Resaj/time2time/fw/t2t_fw/state_machine.cpp

/**********************************************************************
 * Project: Time2time
 * 
 * File description: This code file contains the parameters and 
 * functions for controlling the state machine and the different modes 
 * of the chronometer
 * 
 * Author: Rubén Espino San José
 * Puma Pride Robotics Team
 * 
 * License: Attribution-NonCommercial-ShareAlike 4.0
 * International (CC BY-NC-SA 4.0) 
 *********************************************************************/

/**********************************************************************
 * Includes
 *********************************************************************/

#include "buttons.h"
#include "buzzer.h"
#include "display.h"
#include "espnow_comm.h"
#include "led_rgb.h"
#include "pass_sensor.h"
#include "scheduler.h"
#include "state_machine.h"
#include "supply.h"
#include "t2t_data.h"

/**********************************************************************
 * Defines & enums
 *********************************************************************/

#define BEST_TIME_INIT_VALUE  1000000

enum program_state {
  INIT_STATE,
  MAIN_MENU,
  SET_NUM_LAPS,
  SELECT_END_NODE,
  RUN_MODE,
  COMM_ERROR,
  SHOW_INFO
};

enum program_substate {
  INIT_SUBSTATE,
  SHOW_LINKED_NODE,
  WAIT_FOR_ACTION,
  SEND_MODE_REQUEST,
  WAIT_FOR_CONFIRMATION,
  WAIT_FOR_LAPS_SELECTION,
  WAIT_FOR_NODE_SELECTION,
  WAIT_FOR_START,
  SHOW_TIME_WITHOUT_DETECTION,
  WAIT_FOR_DETECTION,
  SHOW_TIME_DETECTION,
  DETECTED_AND_SENSING_LOCKED,
  DETECTED_AND_SENSING_ACTIVED,
  SHOW_FINAL_TIME,
  FINISHED
};

enum mode2run {
  NORMAL_LAP_TIME_MODE,
  X_LAPS_TIME_MODE,
  TIME_TRIAL_MODE,
  START_STOP_MODE,
  TOAST_MODE,
  SHOW_T2T_INFO,
  ONLY_CHARGE
};

enum nodeSelectionState {
  ERROR_WHILE_SELECTING = -1,
  SELECTION_IN_PROGRESS = 0,
  NODE_SELECTED = 1
};

typedef void (*function)(void);

typedef struct {
  mode2run          time_mode;
  char              text_in_menu[22];
  function          func;
  program_state     next_menu_state;
  program_substate  first_subtate;
} s_mode_data;

/**********************************************************************
 * Local functions declarations
 *********************************************************************/

void show_main_menu(uint8_t group_num);
void normal_lap_time_mode(void);
bool x_laps_time_mode_laps_selection(void);
void x_laps_time_mode(void);
nodeSelectionState end_node_selection(mode2run t2t_mode);
void time_trial_mode(void);
void start_stop_mode(void);
void toast_mode(void);
void show_t2t_info(void);
void set_led_from_diags(bool isModeRunning);
void showSecondaryNodeTime(mode2run t2t_mode, uint16_t time2show);
void go_to_sleep(void);

/**********************************************************************
 * Local variables
 *********************************************************************/

program_substate substate = INIT_SUBSTATE;

static uint16_t x_time_mode_target_laps = 3;
static uint32_t best_time_lap_ms = BEST_TIME_INIT_VALUE;
static uint32_t best_time_total_ms = BEST_TIME_INIT_VALUE;

s_mode_data mode_data[] = {
  /* time_mode           , text_in_menu          , func                 , next_menu_state , first_subtate */
  { NORMAL_LAP_TIME_MODE , "Normal lap time"     , normal_lap_time_mode , RUN_MODE        , INIT_SUBSTATE },
  { X_LAPS_TIME_MODE     , "X laps time"         , x_laps_time_mode     , SET_NUM_LAPS    , INIT_SUBSTATE },
  { TIME_TRIAL_MODE      , "Time trial (2x t2t)" , time_trial_mode      , SELECT_END_NODE , INIT_SUBSTATE },
  { START_STOP_MODE      , "Start/Stop (2x t2t)" , start_stop_mode      , SELECT_END_NODE , INIT_SUBSTATE },
  { TOAST_MODE           , "Get toast time"      , toast_mode           , RUN_MODE        , INIT_SUBSTATE },
  { SHOW_T2T_INFO        , "Time2time info"      , show_t2t_info        , SHOW_INFO       , INIT_SUBSTATE },
  { ONLY_CHARGE          , "Only charge"         , go_to_sleep          , RUN_MODE        , INIT_SUBSTATE }
};

/**********************************************************************
 * Local functions
 *********************************************************************/

/**********************************************************************
 * @brief Shows the main menu with the different t2t options
 * 
 * @param group_num: number of menu options group to display on
 *    the screen
 */
void show_main_menu(uint8_t group_num)
{
  s_display_text text[] = {
    /* text          , pos_X , pos_Y , font      , aligment */
    { "Select mode:" , 0     , 0     , MENU_FONT , ALIGN_LEFT  },
    { ""             , 0     , 15    , MENU_FONT , ALIGN_LEFT  },
    { ""             , 0     , 30    , MENU_FONT , ALIGN_LEFT  },
    { ""             , 0     , 45    , MENU_FONT , ALIGN_LEFT  },
    { ""             , 125   , 45    , MENU_FONT , ALIGN_RIGHT }
  };

  sprintf(text[1].text, "A: %s", mode_data[group_num*2].text_in_menu);
  if((group_num*2 + 1) < sizeof(mode_data)/sizeof(s_mode_data))
    sprintf(text[2].text, "B: %s", mode_data[group_num*2 + 1].text_in_menu);
  else
    sprintf(text[2].text, "");
  if(2 < sizeof(mode_data)/sizeof(s_mode_data))
  {
    sprintf(text[3].text, "C: ...");
    sprintf(text[4].text, "(Pg %u/%u)", group_num+1, (uint8_t)(ceil(((float)sizeof(mode_data)/sizeof(s_mode_data))/2)));
  }
  else
    sprintf(text[3].text, "");

  display_set_data(text, sizeof(text)/sizeof(s_display_text));
}

/**********************************************************************
 * @brief Executes the cyclic time measurement mode and shows the time 
 * of each lap
 */
void normal_lap_time_mode(void)
{
  static uint32_t time_detection = 0;
  static uint32_t time_last_lap_ms = 0;
  static uint32_t time_last_detection = 0;
  static s_display_text text[] = {
    /* Text , pos_X , pos_Y , font                , aligment   */
    {  ""   , 0     , 0     , MAIN_TIME_FONT      , ALIGN_LEFT  },
    {  ""   , 120   , 50    , SECONDARY_TIME_FONT , ALIGN_RIGHT }
  };

  //todo: manage order of the nodes when using more than one to measure the partial times
  //todo: program partial times

  switch(substate)
  {
    case INIT_SUBSTATE:
      /* substate actions */
      set_default_sensor_active_edge();
      
      sprintf(text[0].text, "0.000");
      sprintf(text[1].text, "Ready");
      display_set_data(text, sizeof(text)/sizeof(s_display_text));
      
      ignoreAnyDetectionPending();
      
      /* test substate changes */
      substate = WAIT_FOR_START;
      break;
      
    case WAIT_FOR_START:
      /* substate actions */

      /* test substate changes */
      if(time_detection = getNextTimeDetection())
      {
        time_last_detection = time_detection;
        set_buzzer_mode(SIMPLE_BEEP);
        substate = SHOW_TIME_WITHOUT_DETECTION;
      }
      break;
      
    case SHOW_TIME_WITHOUT_DETECTION:
    {
      /* substate actions */
      uint32_t t_now = 0;
      t_now = get_currentTimeMs();
      sprintf(text[0].text, "%.3f", (t_now - time_last_detection)/1000.0);
      sprintf(text[1].text, "Last lap: %.3f", time_last_lap_ms/1000.0);
      display_set_data(text, sizeof(text)/sizeof(s_display_text));
      
      /* test substate changes */
      if(t_now - time_last_detection > 1000)
      {
        ignoreAnyDetectionPending();
        substate = WAIT_FOR_DETECTION;
      }
      break;
    }
    case WAIT_FOR_DETECTION:
      /* substate actions */
      sprintf(text[0].text, "%.3f", (get_currentTimeMs() - time_last_detection)/1000.0);
      sprintf(text[1].text, "Last lap: %.3f", time_last_lap_ms/1000.0);
      display_set_data(text, sizeof(text)/sizeof(s_display_text));

      /* test substate changes */
      if(time_detection = getNextTimeDetection())
        substate = SHOW_TIME_DETECTION;
      break;
    
    case SHOW_TIME_DETECTION:
      /* substate actions */
      sprintf(text[0].text, "%.3f", (time_detection - time_last_detection)/1000.0);
      sprintf(text[1].text, "Last lap: %.3f", time_last_lap_ms/1000.0);
      display_set_data(text, sizeof(text)/sizeof(s_display_text));

      if((time_detection - time_last_detection) < best_time_lap_ms)
      {
        best_time_lap_ms = time_detection - time_last_detection;
        set_buzzer_mode(DOUBLE_BEEP);
      }
      else
        set_buzzer_mode(SIMPLE_BEEP);
      time_last_lap_ms = time_detection - time_last_detection;
      time_last_detection = time_detection;

      /* test substate changes */
      substate = DETECTED_AND_SENSING_LOCKED;
      break;
      
    case DETECTED_AND_SENSING_LOCKED:
      /* substate actions */

      /* test substate changes */
      if(get_currentTimeMs() - time_last_detection > 1000)
      {
        ignoreAnyDetectionPending();
        substate = DETECTED_AND_SENSING_ACTIVED;
      }
      break;
      
    case DETECTED_AND_SENSING_ACTIVED:
      /* substate actions */

      /* test substate changes */
      if(time_detection = getNextTimeDetection())
        substate = SHOW_TIME_DETECTION;
      else if(get_currentTimeMs() - time_last_detection > 2000)
        substate = WAIT_FOR_DETECTION;
      break;
      
    default:
      break;
  }
}

/**********************************************************************
 * @brief Executes the selection of the number of laps for the 
 * x_laps_time_mode
 * 
 * @returns true if the number of laps has been selected; false if not
 */
bool x_laps_time_mode_laps_selection(void)
{
  static uint16_t target_laps_selection = x_time_mode_target_laps;

  switch(substate)
  {
    case INIT_SUBSTATE:
    {
      /* substate actions */
      s_display_text text[] = {
        /* text                   , pos_X , pos_Y , font          , aligment   */
        { "Select number of laps:", 0     , 0     , MENU_FONT     , ALIGN_LEFT },
        { "A -> +1"               , 0     , 15    , MENU_FONT     , ALIGN_LEFT },
        { "B -> OK"               , 0     , 30    , MENU_FONT     , ALIGN_LEFT },
        { "C -> -1"               , 0     , 45    , MENU_FONT     , ALIGN_LEFT },
        { ""                      , 60    , 10    , MAIN_TIME_FONT, ALIGN_LEFT }
      };
      sprintf(text[4].text, "%u", target_laps_selection);
      display_set_data(text, sizeof(text)/sizeof(s_display_text));

      /* test substate changes */
      substate = WAIT_FOR_LAPS_SELECTION;
      break;
    }
    case WAIT_FOR_LAPS_SELECTION:
      /* substate actions */

      /* test substate changes */
      if(get_button_state(BUTTON_A))
      {
        target_laps_selection++;
        substate = INIT_SUBSTATE;
      }
      else if(get_button_state(BUTTON_B))
      {
        if(target_laps_selection != x_time_mode_target_laps)
        {
          best_time_total_ms = BEST_TIME_INIT_VALUE;
          x_time_mode_target_laps = target_laps_selection;
        }

        return true;
      }
      else if(get_button_state(BUTTON_C))
      {
        target_laps_selection = target_laps_selection > 1 ? target_laps_selection - 1 : target_laps_selection;
        substate = INIT_SUBSTATE;
      }
      break;

    default:
      break;
  }

  return false;
}

/**********************************************************************
 * @brief Executes the cyclic time measurement mode for the number of 
 * selected laps and shows the time of each lap and the total one
 */
void x_laps_time_mode(void)
{
  static uint32_t time_detection = 0;
  static uint32_t time_init = 0;
  static uint32_t time_last_detection = 0;
  static uint16_t laps_to_go = 0;

  static s_display_text text[] = {
    /* text , pos_X , pos_Y , font                , aligment   */
    {  ""   , 0     , 0     , MAIN_TIME_FONT      , ALIGN_LEFT  },
    {  ""   , 120   , 50    , SECONDARY_TIME_FONT , ALIGN_RIGHT }
  };

  //todo: program partial times

  switch(substate)
  {
    case INIT_SUBSTATE:
      /* substate actions */
      laps_to_go = x_time_mode_target_laps;
      set_default_sensor_active_edge();
      
      sprintf(text[0].text, "0.000");
      sprintf(text[1].text, "Ready");
      display_set_data(text, sizeof(text)/sizeof(s_display_text));
      
      ignoreAnyDetectionPending();
      
      /* test substate changes */
      substate = WAIT_FOR_START;
      break;
      
    case WAIT_FOR_START:
      /* substate actions */

      /* test substate changes */
      if(time_detection = getNextTimeDetection())
      {
        time_init = time_detection;
        time_last_detection = time_init;
        set_buzzer_mode(SIMPLE_BEEP);
        substate = SHOW_TIME_WITHOUT_DETECTION;
      }
      break;
      
    case SHOW_TIME_WITHOUT_DETECTION:
    {
      /* substate actions */
      uint32_t t_now = 0;
      t_now = get_currentTimeMs();
      sprintf(text[0].text, "%.3f", (t_now - time_init)/1000.0);
      sprintf(text[1].text, "Laps to go: %u", laps_to_go);
      display_set_data(text, sizeof(text)/sizeof(s_display_text));

      /* test substate changes */
      if(t_now - time_detection > 1000)
      {
        ignoreAnyDetectionPending();
        substate = WAIT_FOR_DETECTION;
      }
    
      break;
    }
    case WAIT_FOR_DETECTION:
    {
      /* substate actions */
      uint32_t t_now = 0;
      t_now = get_currentTimeMs();
      sprintf(text[0].text, "%.3f", (t_now - time_init)/1000.0);
      sprintf(text[1].text, "Laps to go: %u", laps_to_go);
      display_set_data(text, sizeof(text)/sizeof(s_display_text));

      /* test substate changes */
      if(time_detection = getNextTimeDetection())
        substate = SHOW_TIME_DETECTION;
      break;
    }
    case SHOW_TIME_DETECTION:
      /* substate actions */
      laps_to_go--;

      sprintf(text[0].text, "%.3f", (time_detection - time_last_detection)/1000.0);
      sprintf(text[1].text, "Laps to go: %u", laps_to_go);
      display_set_data(text, sizeof(text)/sizeof(s_display_text));

      if((time_detection - time_last_detection) < best_time_lap_ms)
      {
        best_time_lap_ms = time_detection - time_last_detection;
        set_buzzer_mode(DOUBLE_BEEP);
      }
      else
        set_buzzer_mode(SIMPLE_BEEP);

      if(laps_to_go == 0)
      {
        if(time_detection - time_init < best_time_total_ms)
        {
          best_time_total_ms = time_detection - time_init;
          set_buzzer_mode(TRIPLE_BEEP);
        }
        
        set_buzzer_mode(LARGE_BEEP);
      }

      time_last_detection = time_detection;

      /* test substate changes */
      substate = DETECTED_AND_SENSING_LOCKED;
      break;
      
    case DETECTED_AND_SENSING_LOCKED:
      /* substate actions */

      /* test substate changes */
      if(get_currentTimeMs() - time_detection > 1000)
      {
        if(laps_to_go == 0)
          substate = SHOW_FINAL_TIME;
        else
        {
          ignoreAnyDetectionPending();
          substate = DETECTED_AND_SENSING_ACTIVED;
        }
      }
      break;
      
    case DETECTED_AND_SENSING_ACTIVED:
      /* substate actions */

      /* test substate changes */
      if(time_detection = getNextTimeDetection())
        substate = SHOW_TIME_DETECTION;
      else if(get_currentTimeMs() - time_last_detection > 2000)
        substate = WAIT_FOR_DETECTION;
      break;
      
    case SHOW_FINAL_TIME:
      /* substate actions */
      sprintf(text[0].text, "%.3f", (time_detection - time_init)/1000.0);
      sprintf(text[1].text, "Press B to restart");
      display_set_data(text, sizeof(text)/sizeof(s_display_text));

      /* test substate changes */
      substate = FINISHED;
      break;

    case FINISHED:
      /* substate actions */

      /* test substate changes */
      if(get_button_state(BUTTON_B))
        substate = INIT_SUBSTATE;
      break;
      
    default:
      break;
  }
}

/**********************************************************************
 * @brief Executes the selection of the end node for the multi-node
 * modes when a mode needs two nodes to work. The start node is the one
 * that has to select the end node
 * 
 * @param t2t_mode: mode to run after the end node selection
 * @return: -1 if there was an error; 1 if the end node was selected;
 *          0 if not
 */
nodeSelectionState end_node_selection(mode2run t2t_mode)
{
  static uint8_t linkedNodes[8]= {0};
  static uint8_t numLinkedNodes = 0;
  static uint8_t index4SelectedNode = 0;

  switch(substate)
  {
    case INIT_SUBSTATE:
      /* state actions */
      numLinkedNodes = getLinkedNodes(linkedNodes);
      index4SelectedNode = 0;

      /* test state changes */
      substate = SHOW_LINKED_NODE;
      break;
        
    case SHOW_LINKED_NODE:
      /* substate actions */

      /* test substate changes */
      if(numLinkedNodes > 0)
      {
        s_display_text text[] = {
          /* text                 , pos_X , pos_Y , font          , aligment   */
          { "Select the end node:", 0     , 0     , MENU_FONT     , ALIGN_LEFT },
          { "A -> Previous"       , 0     , 15    , MENU_FONT     , ALIGN_LEFT },
          { "B -> OK"             , 0     , 30    , MENU_FONT     , ALIGN_LEFT },
          { "C -> Next"           , 0     , 45    , MENU_FONT     , ALIGN_LEFT },
          { ""                    , 90    , 10    , MAIN_TIME_FONT, ALIGN_LEFT }
        };
        sprintf(text[4].text, "%u", linkedNodes[index4SelectedNode]);
        display_set_data(text, sizeof(text)/sizeof(s_display_text));        
        substate = WAIT_FOR_NODE_SELECTION;
      }
      else
      {
        s_display_text text_error[] = {
          /* text                  , pos_X , pos_Y , font      , aligment   */
          { "Error! No node linked", 0     , 20    , MENU_FONT , ALIGN_LEFT },
          { "Press C to return"    , 0     , 45    , MENU_FONT , ALIGN_LEFT },
        };
        display_set_data(text_error, sizeof(text_error)/sizeof(s_display_text));
        substate = WAIT_FOR_ACTION;
      }
      break;

    case WAIT_FOR_NODE_SELECTION:
      /* substate actions */

      /* test substate changes */
      if(get_button_state(BUTTON_A))
      {
        if(index4SelectedNode > 0)
        {
          index4SelectedNode--;
          substate = SHOW_LINKED_NODE;
        }
      }
      else if(get_button_state(BUTTON_B))
      {
        if(isNodeLinked(linkedNodes[index4SelectedNode]))
          substate = SEND_MODE_REQUEST;
        else
        {
          s_display_text text_error[] = {
            /* text               , pos_X , pos_Y , font      , aligment   */
            { "Error!"            , 0     , 8     , MENU_FONT , ALIGN_LEFT },
            { "Node not available", 0     , 20    , MENU_FONT , ALIGN_LEFT },
            { "Press C to return" , 0     , 45    , MENU_FONT , ALIGN_LEFT },
          };
          display_set_data(text_error, sizeof(text_error)/sizeof(s_display_text));
          substate = WAIT_FOR_ACTION;
        }
      }
      else if(get_button_state(BUTTON_C))
      {
        if(index4SelectedNode < (numLinkedNodes-1))
        {
          index4SelectedNode++;;
          substate = SHOW_LINKED_NODE;
        }
      }
      break;

    case WAIT_FOR_ACTION:
      /* substate actions */

      /* test substate changes */
      if(get_button_state(BUTTON_C))
        return ERROR_WHILE_SELECTING;
      break;

    case SEND_MODE_REQUEST:
      /* substate actions */
      configNodes4WorkingMode(t2t_mode, &linkedNodes[index4SelectedNode], 1);

      /* test substate changes */
      substate = WAIT_FOR_CONFIRMATION;
      break;

    case WAIT_FOR_CONFIRMATION:
    {
      /* substate actions */
      int8_t acceptance = 0;
      acceptance = isAcceptanceCompleted();
      
      /* test substate changes */
      switch(acceptance)
      {
        case ACCEPTANCE_COMPLETED:
          substate = FINISHED;
          break;

        case ACCEPTANCE_REJECTED:
        {
          s_display_text text_error[] = {
            /* text               , pos_X , pos_Y , font      , aligment   */
            { "Error!"            , 0     , 8     , MENU_FONT , ALIGN_LEFT },
            { "No answer received", 0     , 20    , MENU_FONT , ALIGN_LEFT },
            { "Press C to return" , 0     , 45    , MENU_FONT , ALIGN_LEFT },
          };
          display_set_data(text_error, sizeof(text_error)/sizeof(s_display_text));
          substate = WAIT_FOR_ACTION;
          break;
        }
        default:
          // Wait. Do nothing
          break;
      }
      break;
    }
    case FINISHED:
      return NODE_SELECTED;
      break;

    default:
      break;
  }

  return SELECTION_IN_PROGRESS;
}

/**********************************************************************
 * @brief Executes the time trial mode and shows the total time spent
 * on the circuit. This is a multinode mode, which requires two nodes
 * to work.
 * 
 * This mode uses the simple detection to determine the start and stop
 * times.
 */
void time_trial_mode(void)
{
  static uint32_t time_start_ms = 0;
  static uint32_t time_stop_ms = 0;
  static uint32_t best_time_race_ms = BEST_TIME_INIT_VALUE;
  static uint8_t secondaryNodeAddress = 0;

  static s_display_text text[] = {
    /* Text , pos_X , pos_Y , font                , aligment   */
    {  ""   , 0     , 0     , MAIN_TIME_FONT      , ALIGN_LEFT  },
    {  ""   , 120   , 50    , SECONDARY_TIME_FONT , ALIGN_RIGHT }
  };

  switch(substate)
  {
    case INIT_SUBSTATE:
      /* substate actions */
      set_default_sensor_active_edge();
      
      sprintf(text[0].text, "0.000");
      sprintf(text[1].text, "Start ready");
      display_set_data(text, sizeof(text)/sizeof(s_display_text));

      ignoreAnyDetectionPending();

      /* test substate changes */
      substate = WAIT_FOR_START;
      break;

    case WAIT_FOR_START:
      /* substate actions */

      /* test substate changes */
      if(time_start_ms = getNextTimeDetection())
      {
        ignoreAnyDetectionRxPending();
        set_buzzer_mode(SIMPLE_BEEP);
        substate = WAIT_FOR_DETECTION;
      }
      break;
      
    case WAIT_FOR_DETECTION:
      /* substate actions */
      sprintf(text[0].text, "%.3f", (get_currentTimeMs() - time_start_ms)/1000.0);
      sprintf(text[1].text, "Start/Stop running");
      display_set_data(text, sizeof(text)/sizeof(s_display_text));

      /* test substate changes */
      if(time_stop_ms = getNextTimeDetectionRx(&secondaryNodeAddress))
      {
        sendESPNowTimeMsg2MainNode(secondaryNodeAddress, ((time_stop_ms - time_start_ms) < best_time_race_ms)? 2 : 1, time_stop_ms - time_start_ms);
        substate = SHOW_TIME_DETECTION;
      }
      break;

    case SHOW_TIME_DETECTION:
      /* substate actions */
      sprintf(text[0].text, "%.3f", (time_stop_ms - time_start_ms)/1000.0);
      sprintf(text[1].text, "Press A to restart");
      display_set_data(text, sizeof(text)/sizeof(s_display_text));

      if((time_stop_ms - time_start_ms) < best_time_race_ms)
        best_time_race_ms = time_stop_ms - time_start_ms;

      /* test substate changes */
      substate = FINISHED;
      break;

    case FINISHED:
      /* substate actions */

      /* test substate changes */
      if(get_button_state(BUTTON_A))
      {
        sendESPNowTimeMsg2MainNode(secondaryNodeAddress, 0, 0);
        substate = INIT_SUBSTATE;
      }
      break;
      
    default:
      break;
  }
}

/**********************************************************************
 * @brief Executes the start/stop time measurement mode and shows the 
 * total time spent on the circuit. This is a multinode mode, which
 * requires two nodes to work.
 * 
 * This mode uses an active detection to determine the start time,
 * which makes the time starts when the sensor changes from a detecting
 * state to a non-detecting state. The simple detection is used to
 * determine the stop time.
 */
void start_stop_mode(void)
{
  static uint32_t time_start_ms = 0;
  static uint32_t time_stop_ms = 0;
  static uint32_t best_time_race_ms = BEST_TIME_INIT_VALUE;
  static uint8_t secondaryNodeAddress = 0;

  static s_display_text text[] = {
    /* Text , pos_X , pos_Y , font                , aligment   */
    {  ""   , 0     , 0     , MAIN_TIME_FONT      , ALIGN_LEFT  },
    {  ""   , 120   , 50    , SECONDARY_TIME_FONT , ALIGN_RIGHT }
  };

  switch(substate)
  {
    case INIT_SUBSTATE:
      /* substate actions */
      invert_sensor_active_edge();

      sprintf(text[0].text, "0.000");
      sprintf(text[1].text, "Start ready");
      display_set_data(text, sizeof(text)/sizeof(s_display_text));

      ignoreAnyDetectionPending();

      /* test substate changes */
      substate = WAIT_FOR_START;
      break;

    case WAIT_FOR_START:
      /* substate actions */

      /* test substate changes */
      if(time_start_ms = getNextTimeDetection())
      {
        ignoreAnyDetectionRxPending();
        set_buzzer_mode(SIMPLE_BEEP);
        substate = WAIT_FOR_DETECTION;
      }
      break;
      
    case WAIT_FOR_DETECTION:
      /* substate actions */
      sprintf(text[0].text, "%.3f", (get_currentTimeMs() - time_start_ms)/1000.0);
      sprintf(text[1].text, "Start/Stop running");
      display_set_data(text, sizeof(text)/sizeof(s_display_text));

      /* test substate changes */
      if(time_stop_ms = getNextTimeDetectionRx(&secondaryNodeAddress))
      {
        sendESPNowTimeMsg2MainNode(secondaryNodeAddress, ((time_stop_ms - time_start_ms) < best_time_race_ms)? 2 : 1, time_stop_ms - time_start_ms);
        substate = SHOW_TIME_DETECTION;
      }
      break;

    case SHOW_TIME_DETECTION:
      /* substate actions */
      sprintf(text[0].text, "%.3f", (time_stop_ms - time_start_ms)/1000.0);
      sprintf(text[1].text, "Press A to restart");
      display_set_data(text, sizeof(text)/sizeof(s_display_text));

      if((time_stop_ms - time_start_ms) < best_time_race_ms)
        best_time_race_ms = time_stop_ms - time_start_ms;

      /* test substate changes */
      substate = FINISHED;
      break;

    case FINISHED:
      /* substate actions */

      /* test substate changes */
      if(get_button_state(BUTTON_A))
      {
        sendESPNowTimeMsg2MainNode(secondaryNodeAddress, 0, 0);
        substate = INIT_SUBSTATE;
      }
      break;
      
    default:
      break;
  }
}

/**********************************************************************
 * @brief Executes the toast time measurement mode and shows the total
 * time spent on toasting the slice.
 * 
 * This mode uses an active detection to determine the start time,
 * which makes the time starts when the sensor changes from a detecting
 * state to a non-detecting state. The simple detection is used to
 * determine the stop time.
 */
void toast_mode(void)
{
  static uint32_t time_detection = 0;
  static uint32_t time_init = 0;
  static uint32_t best_toast_time_ms = BEST_TIME_INIT_VALUE;

  static s_display_text text[] = {
    /* Text , pos_X , pos_Y , font                , aligment   */
    {  ""   , 0     , 0     , MAIN_TIME_FONT      , ALIGN_LEFT  },
    {  ""   , 120   , 50    , SECONDARY_TIME_FONT , ALIGN_RIGHT }
  };

  switch(substate)
  {
    case INIT_SUBSTATE:
      /* substate actions */
      invert_sensor_active_edge();

      sprintf(text[0].text, "0.000");
      sprintf(text[1].text, "Ready");
      display_set_data(text, sizeof(text)/sizeof(s_display_text));
      
      ignoreAnyDetectionPending();
      
      /* test substate changes */
      substate = WAIT_FOR_START;
      break;
      
    case WAIT_FOR_START:
      /* substate actions */

      /* test substate changes */
      if(time_detection = getNextTimeDetection())
      {
        time_init = time_detection;
        set_default_sensor_active_edge();
        set_buzzer_mode(SIMPLE_BEEP);
        substate = SHOW_TIME_WITHOUT_DETECTION;
      }
      break;
      
    case SHOW_TIME_WITHOUT_DETECTION:
    {
      /* substate actions */
      uint32_t t_now = 0;
      t_now = get_currentTimeMs();
      sprintf(text[0].text, "%.3f", (t_now - time_init)/1000.0);
      sprintf(text[1].text, "Press B to abort");
      display_set_data(text, sizeof(text)/sizeof(s_display_text));

      /* test substate changes */
      if(t_now - time_detection > 1000)
      {
        ignoreAnyDetectionPending();
        substate = WAIT_FOR_DETECTION;
      }

      if(get_button_state(BUTTON_B))
        substate = INIT_SUBSTATE;

      break;
    }
    case WAIT_FOR_DETECTION:
    {
      /* substate actions */
      uint32_t t_now = 0;
      t_now = get_currentTimeMs();
      sprintf(text[0].text, "%.3f", (t_now - time_init)/1000.0);
      sprintf(text[1].text, "Press B to abort");
      display_set_data(text, sizeof(text)/sizeof(s_display_text));

      /* test substate changes */
      if(time_detection = getNextTimeDetection())
        substate = SHOW_FINAL_TIME;

      if(get_button_state(BUTTON_B))
        substate = INIT_SUBSTATE;

      break;
    }
    case SHOW_FINAL_TIME:
      /* substate actions */
      sprintf(text[0].text, "%.3f", (time_detection - time_init)/1000.0);
      sprintf(text[1].text, "Press B to restart");
      display_set_data(text, sizeof(text)/sizeof(s_display_text));

      if(time_detection - time_init < best_toast_time_ms)
      {
        best_toast_time_ms = time_detection - time_init;
        set_buzzer_mode(TRIPLE_BEEP);
      }
      
      set_buzzer_mode(LARGE_BEEP);

     /* test substate changes */
      substate = FINISHED;
      break;

    case FINISHED:
      /* substate actions */

      /* test substate changes */
      if(get_button_state(BUTTON_B))
        substate = INIT_SUBSTATE;
      break;
      
    default:
      break;
  }
}

/**********************************************************************
 * @brief Shows the information related to the t2t node
 */
void show_t2t_info(void)
{
  static uint32_t time_init = 0;

  switch(substate)
  {
    case INIT_SUBSTATE:
    {
      /* substate actions */
      uint8_t textSize = 0;
      uint8_t MAClisted = false;
      uint8_t linkedNodes[8];
      uint8_t numLinkedNodes;

      s_display_text text[] = {
        /* Text , pos_X , pos_Y , font                , aligment      */
        {  ""   , 63    , 0     , SECONDARY_TIME_FONT , ALIGN_CENTER  },
        {  ""   , 63    , 12    , SECONDARY_TIME_FONT , ALIGN_CENTER  },
        {  ""   , 0     , 24    , SECONDARY_TIME_FONT , ALIGN_LEFT    },
        {  ""   , 0     , 36    , SECONDARY_TIME_FONT , ALIGN_LEFT    },
        {  ""   , 0     , 48    , SECONDARY_TIME_FONT , ALIGN_LEFT    }
      };
      sprintf(text[0].text, "T2T #%u info -- %s", getThisNodeAddr(), FW_VERSION);
      MAClisted = getNcheckMACAddr(text[1].text);

      if(MAClisted)
      {
        numLinkedNodes = getLinkedNodes(linkedNodes);

        if(numLinkedNodes > 0)
        {
          sprintf(text[2].text, "Linked T2Ts: ");
          textSize = strlen(text[2].text);
          for(uint8_t index=0; index<numLinkedNodes; index++)
          {
            text[2].text[textSize] = (char)(linkedNodes[index]+48);
            textSize++;
          }
        }
        else
          sprintf(text[2].text, "Linked T2Ts: None");
      }
      else
        sprintf(text[2].text, "Linked T2Ts: -");

      sprintf(text[3].text, "Battery voltage: %.2fV", g_batt_voltage/1000.0);
      switch(batt_charger_diag)
      {
        case TEMP_OR_TIMER_FAULT: // 0 - Temperature fault or timer fault
          sprintf(text[4].text, "PW: temp/timer fault");
          break;
          
        case PRECONDITIONING:     // 2 - Preconditioning, constant current or constant voltage
          sprintf(text[4].text, "PW: charging battery");
          break;
          
        case LOW_BATTERY_OUTPUT:  // 3 - Low battery output
          sprintf(text[4].text, "PW: low battery");
          break;
          
        case CHARGE_COMPLETE:     // 4 - Charge complete
          sprintf(text[4].text, "PW: USB-powered");
          break;
          
        case NO_BATTERY:          // 6 - Shutdown (VDD = VIN) or no battery present
          sprintf(text[4].text, "PW: no battery");
          break;
          
        case NO_INPUT_POWER:      // 7 - Shutdown (VDD = VBAT) or no input power present
          sprintf(text[4].text, "PW: battery-powered");
          break;
          
        default:
          sprintf(text[4].text, "PW: no info");
          break;
      }

      display_set_data(text, sizeof(text)/sizeof(s_display_text));
      time_init = get_currentTimeMs();

      /* test substate changes */
      substate = FINISHED;
      break;
    }
    case FINISHED:
      /* substate actions */

      /* test substate changes */
      if(get_currentTimeMs() - time_init >= 3000)
        substate = INIT_SUBSTATE;
      break;

    default:
      break;
  }
}

/**********************************************************************
 * @brief Set the status of the led according to the supply
 * diagnostics. If a mode is running, the led blink is a sinusoidal
 * wave.
 * 
 * @param isModeRunning: true if a mode is running; false if not
 */
void set_led_from_diags(bool isModeRunning)
{
  e_rgb_color rgb_color;
  uint16_t brightness = 0, period = 0, period_on = 0;

  if(batt_charger_diag == TEMP_OR_TIMER_FAULT) // 0 - Temperature fault or timer fault
  {
    set_rgb_led_blink_mode(RGB_RED, MAX_BRIGHTNESS, 200, 100);
    return;
  }
  
  switch(batt_charger_diag)
  {
    case PRECONDITIONING:     // 2 - Preconditioning, constant current or constant voltage
      rgb_color = RGB_YELLOW;
      brightness = MAX_BRIGHTNESS;
      period = 2000;
      period_on = 100;
      break;
      
    case LOW_BATTERY_OUTPUT:  // 3 - Low battery output
      rgb_color = RGB_RED;
      brightness = MAX_BRIGHTNESS;
      period = 2000;
      period_on = 100;
      break;
      
    case CHARGE_COMPLETE:     // 4 - Charge complete
      rgb_color = RGB_GREEN;
      brightness = MAX_BRIGHTNESS;
      period = 2000;
      period_on = 100;
      break;
      
    case NO_BATTERY:          // 6 - Shutdown (VDD = VIN) or no battery present
      rgb_color = RGB_BLUE;
      brightness = MAX_BRIGHTNESS;
      period = 2000;
      period_on = 2000;
      break;
      
    case NO_INPUT_POWER:      // 7 - Shutdown (VDD = VBAT) or no input power present
      rgb_color = RGB_CYAN;
      brightness = MAX_BRIGHTNESS;
      period = 2000;
      period_on = 100;
      break;
      
    default:
      break;
  }

  if(!brightness)
    set_rgb_led_off_mode();
  else if(period == period_on)
    set_rgb_led_on_mode(rgb_color, brightness);
  else
  {
    if(isModeRunning)
      set_rgb_led_sinusoidal_wave_mode(rgb_color, brightness, period, period_on*5);
    else
      set_rgb_led_blink_mode(rgb_color, brightness, period, period_on);
  }
}


/**********************************************************************
 * @brief Show the time in the secondary node if any time has been
 * received from the main node
 * 
 * @param t2t_node: running mode
 * @param time2show: time to show in milliseconds
 */
void showSecondaryNodeTime(mode2run t2t_mode, uint16_t time2show)
{
  s_display_text timeText[] = {
    /* Text , pos_X , pos_Y , font                , aligment   */
    {  ""   , 0     , 0     , MAIN_TIME_FONT      , ALIGN_LEFT  },
    {  ""   , 120   , 50    , SECONDARY_TIME_FONT , ALIGN_RIGHT }
  };

  if(time2show > 0)
  {
    switch(t2t_mode)
    {
      case NORMAL_LAP_TIME_MODE:
        //todo: fill
        break;

      case X_LAPS_TIME_MODE:
        //todo: fill
        break;

      case TIME_TRIAL_MODE:
      case START_STOP_MODE:
        sprintf(timeText[0].text, "%.3f", time2show/1000.0);
        sprintf(timeText[1].text, "Final time");
        display_set_data(timeText, sizeof(timeText)/sizeof(s_display_text));
        break;

      default:
        /* Do nothing */
        break;
    }
  }
}

/**********************************************************************
 * @brief Go-to-sleep function. The node goes to sleep and the
 * peripherals are disabled to avoid conmsumption and let a faster
 * charge of the battery.
 */
void go_to_sleep(void)
{
  static s_display_text text[] = {
    /* Text , pos_X , pos_Y , font                , aligment   */
    {  ""   , 0     , 0     , SECONDARY_TIME_FONT , ALIGN_LEFT }
  };

  display_set_data(text, sizeof(text)/sizeof(s_display_text));
  display_task();
  disable_pass_sensor(LOCK_POWER_12V_PIN);
  esp_deep_sleep_start();
}

/**********************************************************************
 * Global functions
 *********************************************************************/

/**********************************************************************
 * @brief Controls the state machine, which selects the different modes 
 * of the chronometer and the states of each one. This function has to 
 * be called periodically through an scheduler
 */
void state_machine_task(void)
{
  static bool isMainNode = true, wasMainNode = true;
  static program_state state = INIT_STATE, prev_state = INIT_STATE;
  static mode2run t2t_mode = NORMAL_LAP_TIME_MODE;
  static uint8_t menu_screen_num = 0;

  isMainNode = isThisTheMainNode();

  if(isMainNode != wasMainNode)
  {
    if(isMainNode)
      state = INIT_STATE; // Reset the state while the node is released from a secondary rol
    else
    {
      s_display_text text[] = {
        /* Text             , pos_X , pos_Y , font      , aligment   */
        {  "Secondary node" , 0     , 8     , MENU_FONT , ALIGN_LEFT  },
        {  "Ready to start" , 0     , 22    , MENU_FONT , ALIGN_LEFT  },
      };
      display_set_data(text, sizeof(text)/sizeof(s_display_text));
      t2t_mode = (mode2run)getMode2Join();
    }
    wasMainNode = isMainNode;
  }

  if(isMainNode) // This node is not being controlled by another one
  {
    /* Main state machine control */
    switch(state)
    {
      case INIT_STATE:
        /* state actions */
        show_main_menu(menu_screen_num);

        /* test state changes */
        state = MAIN_MENU;
        break;

      case MAIN_MENU:
        /* state actions */
        
        /* test state changes */
        if(get_button_state(BUTTON_A))
        {
          t2t_mode = mode_data[menu_screen_num*2].time_mode;
          state = mode_data[menu_screen_num*2].next_menu_state;
          substate = mode_data[menu_screen_num*2].first_subtate;
        }
        else if(get_button_state(BUTTON_B))
        {
          if((menu_screen_num*2 + 1) < sizeof(mode_data)/sizeof(s_mode_data))
          {
            t2t_mode = mode_data[menu_screen_num*2 + 1].time_mode;
            state = mode_data[menu_screen_num*2 + 1].next_menu_state;
            substate = mode_data[menu_screen_num*2 + 1].first_subtate;
          }
        }
        else if(get_button_state(BUTTON_C))
        {
          if(2 < sizeof(mode_data)/sizeof(s_mode_data))
          {
            menu_screen_num++;
            menu_screen_num = menu_screen_num % (uint8_t)(ceil(((float)sizeof(mode_data)/sizeof(s_mode_data))/2));
            state = INIT_STATE;
          }
        }
        break;

      case SET_NUM_LAPS:
        /* state actions */

        /* test state changes */
        if(x_laps_time_mode_laps_selection())
          state = RUN_MODE;
        break;

      case SELECT_END_NODE:
      {
        /* state actions */
        nodeSelectionState nodeSelState;
        nodeSelState = end_node_selection(t2t_mode);

        /* test state changes */
        if(NODE_SELECTED == nodeSelState)
          state = RUN_MODE;
        else if(ERROR_WHILE_SELECTING == nodeSelState)
          state = INIT_STATE;
        break;
      }
      case RUN_MODE:
        /* state actions */
        (*mode_data[t2t_mode].func)();

        /* test state changes */
        if(get_button_state(BUTTON_C))
        {
          set_default_sensor_active_edge();
          releaseWorkingModeComm();
          state = INIT_STATE;
        }
        else if(!isEveryWorkingNodeLinked())
        {
          s_display_text text_error[] = {
            /* text                 , pos_X , pos_Y , font      , aligment   */
            { "Error! Comm failed!" , 0     , 20    , MENU_FONT , ALIGN_LEFT },
            { "Press C to return"   , 0     , 45    , MENU_FONT , ALIGN_LEFT },
          };
          display_set_data(text_error, sizeof(text_error)/sizeof(s_display_text));

          set_default_sensor_active_edge();
          releaseWorkingModeComm();
          state = COMM_ERROR;
        }
        break;

      case COMM_ERROR:
        /* state actions */

        /* test state changes */
        if(get_button_state(BUTTON_C))
          state = INIT_STATE;
        break;

      case SHOW_INFO:
        /* state actions */
        (*mode_data[t2t_mode].func)();

        /* test state changes */
        if(get_button_state(BUTTON_C))
          state = INIT_STATE;
        break;
      
      default:
        break;
    }

    /* Check if a mode is running and set this node as busy */
    if(state != prev_state)
    {
      if(RUN_MODE == state)
      {
        setThisNodeAsBusy();
        substate = INIT_SUBSTATE;
      }
      
      prev_state = state;
    }
  }
  else // This node is being controlled by another one
  {
    uint8_t beep = 0;
    int32_t time2show = getTime2show(&beep);
    
    if(isAnyDetectionPending())
    {
      switch(t2t_mode)
      {
        case NORMAL_LAP_TIME_MODE:
        case X_LAPS_TIME_MODE:
        case TIME_TRIAL_MODE:
        case START_STOP_MODE:
          sendDetectionMsg(getNextTimeDetection());
          break;
  
        default:
          /* Do nothing */
          break;
      }
    }

    if(time2show > 0)
    {
      showSecondaryNodeTime(t2t_mode, time2show);
      if(beep == 1)
        set_buzzer_mode(SIMPLE_BEEP);
      else if (beep == 2)
        set_buzzer_mode(DOUBLE_BEEP);
    }
    else if(time2show == 0)
    {
      s_display_text text[] = {
        /* Text             , pos_X , pos_Y , font      , aligment   */
        {  "Secondary node" , 0     , 8     , MENU_FONT , ALIGN_LEFT  },
        {  "Ready to start" , 0     , 22    , MENU_FONT , ALIGN_LEFT  },
      };
      display_set_data(text, sizeof(text)/sizeof(s_display_text));
    }

    if(!isMainNodeLinked()) // If comm with main node is lost, exit from mode
      releaseWorkingModeComm();
  }

  /* General function for the RGB led control */
  set_led_from_diags(state == RUN_MODE || !isMainNode);
}
