Resaj/time2time/fw/t2t_fw/espnow_comm.cpp

/**********************************************************************
 * Project: Time2time
 * 
 * File description: This code file contains the parameters and 
 * functions for for the ESP-Now communication between ESP32 modules
 * 
 * Author: Rubén Espino San José
 * Puma Pride Robotics Team
 * 
 * License: Attribution-NonCommercial-ShareAlike 4.0
 * International (CC BY-NC-SA 4.0) 
 *********************************************************************/

/**********************************************************************
 * Includes
 *********************************************************************/

#include <esp_now.h>
#include <WiFi.h>
#include "config/PINSEL.h"
#include "config/MyMACAddrList.h"
#include "espnow_comm.h"
#include "led_rgb.h"
#include "scheduler.h"

/**********************************************************************
 * Defines & enums
 *********************************************************************/

#define MAX_MSG_SIZE 4

/**********************************************************************
 * Structs
 *********************************************************************/

typedef struct s_t2t_node {
  uint8_t   nodeAddress;    // Node address. Defined by the jumpers on the board, between 0 and 7
  uint8_t   *MACAddr;       // MAC address of the ESP node
  bool      linked;         // Linked flag
  bool      working;        // Working flag. Indicates wether the node is being used in the working mode
  uint32_t  lastTxTime_ms;  // Last time that a message has been transmitted to the remote node
  uint32_t  lastRxTime_ms;  // Last time that a message has been received from the remote node
} s_t2t_node;

typedef struct {
  uint8_t nodeAddr  : 4;
  uint8_t msgLength : 4;
  uint8_t msg[MAX_MSG_SIZE];
  uint32_t rxTime;
} s_rxBuffer;

typedef struct {
  uint8_t nodeAddr;
  uint32_t detectionTime;
} s_detectionBuff;

typedef struct {
  uint8_t type  : 3;
  uint8_t info  : 5;
} s_espnow_default_msg;

typedef struct {
  uint8_t type        : 3;
  uint8_t ack         : 1;  // ACK or ask for it. 1 = true; 0 = false
  uint8_t reserved    : 4;
} s_espnow_link_msg;

typedef struct {
  uint32_t type       : 3;
  uint32_t work_mode  : 3;  // Working mode (0-7)
  uint32_t request    : 1;  // Request from main (1), answer to accept from secondary (0) or release node from main (0)
  uint32_t reserved1  : 1;
  uint32_t ref_time   : 11; // Reference time in milliseconds. Up to 2 seconds
  uint32_t reserved2  : 5;
} s_espnow_mode_msg;

typedef struct {
  uint8_t type        : 3;
  uint8_t reserved    : 5;
  uint8_t elapsed_time;     // Elapsed time between the detection and the tx of the msg, in ms
} s_espnow_detection_msg;

typedef struct {
  uint8_t type          : 3;
  uint8_t beep          : 2;  // No beep (0), simple beep (1) or double beep (2) when receiving the order
  uint8_t time2show_min : 3;  // Partial time in minutes. Up to 7 minutes
  uint16_t time2show_msec;    // Partial time in milliseconds. Up to 59999 milliseconds
} s_espnow_time_msg;

typedef struct {
  uint8_t type        : 3;
  uint8_t lowBatt     : 1;  // Low battery flag. 1 = true; 0 = false
  uint8_t battVoltage : 4;  // Sent as: (batt_volt – 2.7) * 10 where 3V < batt_volt < 4.2V
} s_espnow_lowBattery_msg;

/**********************************************************************
 * Defines & enums
 *********************************************************************/

typedef enum {
  LINK_MSG,
  MODE_MSG,
  DETECTION_MSG,
  TIME_MSG,
  LOWBATTERY_MSG
} msg_type;

/**********************************************************************
 * Local variables
 *********************************************************************/

uint32_t t_origen_ms = 0;                 // Origin time to reference the initial linking and enable it again after leaving a working mode
const uint8_t nNodes = sizeof(MyMACAddrList)/sizeof(MyMACAddrList[0]); // Number of nodes available in the MAC list
s_t2t_node t2t_node[nNodes];              // Matrix to store the information of the nodes. Up to 8 nodes
s_t2t_node *thisNode = NULL;              // Pointer to the node position at t2t_node
s_t2t_node *mainNode = NULL;              // Pointer to the main node position at t2t_node
                                          // Determines the node that manages the total times and the functionament mode
                                          // It it set when selecting the functionament mode.
s_rxBuffer rxBuffer[8];                   // Cyclic buffer to store the received messages
uint8_t nextMsgBuff2write = 0;            // Next byte to write in the rx buffer
uint8_t nextMsgBuff2read = 0;             // Next byte to read from the rx buffer

uint8_t mode2join = 0;                    // Mode to join when a request must be sent
int8_t flag_modeReq[nNodes];              // Variable to save the mode message request. 1 for waiting accceptance; 0 is nothing
bool modeRejected = false;                // Variable to indicate when a mode has been rejected by at least one of the remote nodes

uint32_t detection_time = 0;              // Detection time to send to the main node
bool detection_waiting4response = false;  // Flag to manage the retransmissions of the detection_time
uint32_t last_detectionMsg_Tx = 0;        // Last time when a detection message was sent
uint32_t time2show = 0;                   // Time to show when a time message is received from the main node
uint8_t beep = 0;                         // Sound to make by the secondary node when a time message is received
bool flag_timeRx = false;                 // Flag to set when a time is received from the main node

s_detectionBuff bufferDetectionMsgRx[7];  // Cyclic buffer to store the times of the detections received
uint8_t nextDetRx2write = 0;              // Next time to write in the storaging buffer
uint8_t nextDetRx2read = 0;               // Next time to read from the storaging buffer

/**********************************************************************
 * Local function declarations
 *********************************************************************/

uint8_t read_moduleNumber(void);
int8_t isMacAddressListed(uint8_t *mac);
void init_node_data(uint8_t nodeAddress);
uint8_t config_node(void);
void OnDataSent(const uint8_t *MAC_Addr, esp_now_send_status_t state);
void OnDataRecv(const uint8_t *MAC_Addr, const uint8_t *receivedData, int32_t len);
void sendESPNowLinkMsg(uint8_t nodeAddress, bool ack);
void sendESPNowModeMsg(uint8_t nodeAddress, uint8_t work_mode, bool request);
void sendESPNowDetectionMsg2MainNode(uint32_t detection_time);
void linking_management(void);
void mode_request_management(void);
void setThisNodeAsIdle(void);
void detection_time_management(void);

/**********************************************************************
 * Local functions
 *********************************************************************/

/**********************************************************************
 * @brief Read the number/address of the node from the peripherals.
 * 
 * @return: number of the node. Range [0..7]
 */
uint8_t read_moduleNumber(void)
{
  uint8_t add_bit1 = digitalRead(PIN_JP_ADD1);
  uint8_t add_bit2 = digitalRead(PIN_JP_ADD2);
  uint8_t add_bit3 = digitalRead(PIN_JP_ADD3);
  return (add_bit1<<2) + (add_bit2<<1) + (add_bit3);
}

/**********************************************************************
 * @brief Checks if the MAC address is listed in MyMACAddrList.
 * 
 * @param mac: MAC address of the node
 * @return: the position in the list if the address is found; -1 if not
 */
int8_t isMacAddressListed(uint8_t *mac)
{
  for(int8_t index=0; index<nNodes; index++)
  {
    bool isEqual = true;

    for(uint8_t pos=0; pos<sizeof(MyMACAddrList[0])/sizeof(uint8_t); pos++)
    {
      if(mac[pos] != MyMACAddrList[index][pos])
      {
        isEqual = false;
        break;
      }
    }
    
    if(isEqual)
      return index;
  }

  return -1;
}

/**********************************************************************
 * @brief Initialyze the data of the specified node in the s_t2t_node
 * struct and mode request buffer
 * 
 * @param nodeAddress: address of the remote node. Range: [0..7]
 */
void init_node_data(uint8_t nodeAddress)
{
  t2t_node[nodeAddress].nodeAddress = nodeAddress;
  t2t_node[nodeAddress].MACAddr = MyMACAddrList[nodeAddress];
  t2t_node[nodeAddress].linked = false;
  t2t_node[nodeAddress].working = false;
  t2t_node[nodeAddress].lastTxTime_ms = 0;
  t2t_node[nodeAddress].lastRxTime_ms = 0;

  flag_modeReq[nodeAddress] = 0;
}

/**********************************************************************
 * @brief ESPNow node configuration. This function reads the node
 * addresses and returns wether or not the node is in the MAC address
 * list.
 * 
 * @return: 0 if the MAC address is in the list and in the right 
 *          position; -1 if the MAC is not founded; -2 if the MAC is in
 *          the wrong position
 */
uint8_t config_node(void)
{
  uint8_t thisNodeAddr = 0;
  uint8_t MACAddr[6];
  int8_t pos = -1;
  
  pinMode(PIN_JP_ADD1, INPUT);
  pinMode(PIN_JP_ADD2, INPUT);
  pinMode(PIN_JP_ADD3, INPUT);

  thisNodeAddr = read_moduleNumber();

  WiFi.macAddress(MACAddr);
  pos = isMacAddressListed(MACAddr);

  if(pos < 0)
    return -1;
  else if(thisNodeAddr != pos)
    return -2;

  init_node_data(thisNodeAddr);

  thisNode = &t2t_node[thisNodeAddr];
  mainNode = &t2t_node[thisNodeAddr];

  return 0;
}

/**********************************************************************
 * @brief Handler executed when there is a ESPNow transmission
 */
void OnDataSent(const uint8_t *MAC_Addr, esp_now_send_status_t state)
{
  int8_t posNodeInList = isMacAddressListed((uint8_t *)MAC_Addr);
  if(posNodeInList >= 0)
    t2t_node[posNodeInList].lastTxTime_ms = get_currentTimeMs(); // Save tx time
}

/**********************************************************************
 * @brief Handler executed when there is a ESPNow reception. Copy the
 * received message to an internal buffer to save the information.
 */
void OnDataRecv(const uint8_t *MAC_Addr, const uint8_t *receivedData, int32_t len)
{
  uint32_t t_now = get_currentTimeMs();
  int8_t posNodeInList = isMacAddressListed((uint8_t *)MAC_Addr);

  if(posNodeInList != -1)
  {
    // Save incoming message in the buffer
    rxBuffer[nextMsgBuff2write].nodeAddr = posNodeInList;
    rxBuffer[nextMsgBuff2write].msgLength = len;
    rxBuffer[nextMsgBuff2write].rxTime = t_now;
    for(int8_t index=0; index<len; index++)
      rxBuffer[nextMsgBuff2write].msg[index] = receivedData[index];
      
    nextMsgBuff2write++;
    nextMsgBuff2write = nextMsgBuff2write % (sizeof(rxBuffer)/sizeof(s_rxBuffer));
  }
}

/**********************************************************************
 * @brief Sends an ESPNow message to link or maintain the communication
 * with another node
 * 
 * @param nodeAddress: address of the remote node. Range: [0..7]
 * @param ack: if the message is sent by the main node, this flag
 *             requires or not an ACK; if the message is sent by a
 *             secondary node, this flag answer with or without the ACK
 */
void sendESPNowLinkMsg(uint8_t nodeAddress, bool ack)
{
  s_espnow_link_msg msg;
  msg.type = (uint8_t)LINK_MSG;
  msg.ack = ack ? 1u : 0u;
  
  (void)esp_now_send(t2t_node[nodeAddress].MACAddr, (uint8_t *) &msg, sizeof(msg));
}

/**********************************************************************
 * @brief Sends an ESPNow message to set the mode of a remote linked
 * node.
 * 
 * @param nodeAddress: address of the remote node. Range: [0..7]
 * @param work_mode: working mode. Range [0..7]
 * @param request: Request from main (1), answer to accept from
 *                 secondary (0) or release node from main (0)
 */
void sendESPNowModeMsg(uint8_t nodeAddress, uint8_t work_mode, bool request)
{
  s_espnow_mode_msg msg;
  msg.type = (uint8_t)MODE_MSG;
  msg.work_mode = work_mode;
  msg.request = request;
  msg.ref_time = (uint16_t)(get_currentTimeMs() % get_led_period());

  (void)esp_now_send(t2t_node[nodeAddress].MACAddr, (uint8_t *) &msg, sizeof(msg));
}

/**********************************************************************
 * @brief Sends an ESPNow message to the main node with the sensor time
 * detection. Only called by a secondary node. It requires an answer
 * message with the time to show.
 * 
 * @param detection_time: time of detection in milliseconds
 */
void sendESPNowDetectionMsg2MainNode(uint32_t detection_time)
{
  s_espnow_detection_msg msg;
  msg.type = (uint8_t)DETECTION_MSG;
  msg.elapsed_time = (uint8_t)(get_currentTimeMs() - detection_time);

  (void)esp_now_send(mainNode->MACAddr, (uint8_t *) &msg, sizeof(msg));
}

/**********************************************************************
 * @brief Manage the linking messages to maintain the communication
 * with the other nodes alive. This function is called periodically
 * when the node is the main one.
 */
void linking_management(void)
{
  uint32_t t_now = 0;
  t_now = get_currentTimeMs();

  // Check the communication with the other nodes is alive
  for(uint8_t index=0; index<nNodes; index++)
  {
    if(&t2t_node[index] != thisNode && t2t_node[index].working == thisNode->working) // Both nodes are in the same mode (working or released)
    {
      // When this node is waiting orders in the main menu, send link periodical messages
      if(!thisNode->working && (t2t_node[index].linked || t_now - t_origen_ms < 4500))
      {
        if(t_now - t2t_node[index].lastRxTime_ms > 4500 && t_now - t_origen_ms > 4500)
          t2t_node[index].linked = false;
        else if(t_now - t2t_node[index].lastTxTime_ms > 2000)
          sendESPNowLinkMsg(index, false);
      }
      
      // When this node is working in a mode with multiple nodes, send link messages if there is no communication in the last 2 seconds
      else if(thisNode->working)
      {
        if(t_now - t2t_node[index].lastRxTime_ms > 4500)
          t2t_node[index].linked = false;
        else if((t_now - t2t_node[index].lastRxTime_ms > 2000 || t_now - t2t_node[index].lastTxTime_ms > 2000) && thisNode == mainNode)
          sendESPNowLinkMsg(index, true); // Request ACK. The secondary node won't answer with link messages if it's not required
      }
    }
  }
}

/**********************************************************************
 * @brief Send mode requests and manage the acceptances for that
 * requests. This function is called periodically when the node is the
 * main one.
 */
void mode_request_management(void)
{
  enum mode_acceptance_state {
    SEND_REQUEST,
    WAIT4RESPONSE,
    CONNECTION_ERROR,
    NO_ACCEPTANCES_PENDING
  };

  static mode_acceptance_state accept_state = NO_ACCEPTANCES_PENDING;
  static uint32_t t_last_mode_msg_sent = 0;
  static uint8_t numAttempts = 0;

  switch(accept_state)
  {
    case SEND_REQUEST:
      /* substate actions */
      for(uint8_t index=0; index<nNodes; index++)
      {
        if(&t2t_node[index] != thisNode && flag_modeReq[index])
          sendESPNowModeMsg(index, mode2join, 1);
      }
      numAttempts++;
      t_last_mode_msg_sent = get_currentTimeMs();

      /* test substate changes */
      accept_state = WAIT4RESPONSE;
      break;

    case WAIT4RESPONSE:
      /* substate actions */

      /* test substate changes */
      switch(isAcceptanceCompleted())
      {
        case ACCEPTANCE_UNCOMPLETED:
          if(get_currentTimeMs() - t_last_mode_msg_sent >= 100)
          {
            if(numAttempts >= 3)
              accept_state = CONNECTION_ERROR;
            else
              accept_state = SEND_REQUEST;
          }
          break;
          
        case ACCEPTANCE_COMPLETED:
          //setThisNodeAsBusy();
          accept_state = NO_ACCEPTANCES_PENDING;
          break;

        default:
          accept_state = CONNECTION_ERROR;
          break;
      }
      break;
      
    case CONNECTION_ERROR:
      /* substate actions */
      modeRejected = true;
      releaseWorkingModeComm();
      for(uint8_t index=0; index<nNodes; index++)
        flag_modeReq[index] = 0;

      /* test substate changes */
      accept_state = NO_ACCEPTANCES_PENDING;
      break;
      
    case NO_ACCEPTANCES_PENDING:
      /* substate actions */
      numAttempts = 0;
      for(uint8_t index=0; index<nNodes; index++)
      {
        if(&t2t_node[index] != thisNode && flag_modeReq[index])
        {
          sendESPNowModeMsg(index, mode2join, 1);
          numAttempts = 1;
        }
      }

      /* test substate changes */
      if(numAttempts == 1)
      {
        t_last_mode_msg_sent = get_currentTimeMs();
        accept_state = WAIT4RESPONSE;
      }
      break;
      
    default:
      break;
  }
}

/**********************************************************************
 * @brief Set this node as idle by clearing the working flag
 */
void setThisNodeAsIdle(void)
{
  thisNode->working = false;
}

/**********************************************************************
 * @brief Send detection time retransmissions if no answer is received.
 * Retry until receiving an answer, up to 7 retransmissions. This
 * function is called periodically when the node is secondary.
 */
void detection_time_management(void)
{
  static uint8_t retx_attempts = 0;
  
  if(detection_waiting4response && (get_currentTimeMs() - last_detectionMsg_Tx) >= 20)
  {
    if(retx_attempts == 7)
    {
      //mainNode->linked = false;
      detection_waiting4response = false;
    }
    else
    {
      sendESPNowDetectionMsg2MainNode(detection_time);
      last_detectionMsg_Tx = get_currentTimeMs();
      retx_attempts++;
    }
  }
  else if(!detection_waiting4response)
    retx_attempts = 0;
}

/**********************************************************************
 * Global functions
 *********************************************************************/

/**********************************************************************
 * @brief ESPNow initialization. This function configures de node,
 * initializes the ESPNow communication and tries to link with the nodes
 * in the MAC list.
 */
void espnow_comm_init(void)
{
  if(config_node() != 0)
    return; // Node not found in the list or wrong placed. Avoid Wi-Fi initialization

  WiFi.mode(WIFI_STA);

  if (esp_now_init() != ESP_OK){
    return; // ESP_now not initialyzed. Avoid linking the nodes
  }

  esp_now_register_send_cb(OnDataSent);
  esp_now_register_recv_cb(OnDataRecv);

  for(uint8_t index=0; index<nNodes; index++)
  {
    if(index != thisNode->nodeAddress)
    {
      init_node_data(index);
      esp_now_peer_info_t peerInfo = {};
      memcpy(peerInfo.peer_addr, MyMACAddrList[index], 6);
      peerInfo.channel = 0;
      peerInfo.encrypt = false;
      if(esp_now_add_peer(&peerInfo) != ESP_OK)
        return;
    }
  }
}

/**********************************************************************
 * @brief Returns the number of listed nodes
 * 
 * @return: number of listed nodes. Range: [0..7]
 */
uint8_t getNumberOfNodes(void)
{
  return nNodes;
}

/**********************************************************************
 * @brief Returns the number/address of this node.
 * 
 * @return: number of the node. Range [0..7]
 */
uint8_t getThisNodeAddr(void)
{
  return thisNode->nodeAddress;
}

/**********************************************************************
 * @brief Returns the MAC address of this node if it is listed in the
 * configuration.
 * 
 * @param macAddr: char array to store the MAC address
 * @return: true is the MAC address has been listed; false if not
 */
bool getNcheckMACAddr(char macAddr[18])
{
  if(NULL != t2t_node[thisNode->nodeAddress].MACAddr)
  {
    WiFi.macAddress().toCharArray(macAddr, 18);
    return true;
  }
  else
  {
    sprintf(macAddr, "MAC bad or not listed");
    return false;
  }
}

/**********************************************************************
 * @brief Returns wether or not this is the main node.
 * 
 * @return: true if this is the main node; false if not
 */
bool isThisTheMainNode(void)
{
  return (thisNode == mainNode);
}

/**********************************************************************
 * @brief Returns the amount of linked nodes and saves in the array
 * passed as reference which their are.
 * 
 * @return: number of linked nodes. Range: [0..total-1]. The actual
 *          node can't be counted
 */
uint8_t getLinkedNodes(uint8_t *nodes)
{
  uint8_t linkedNodes = 0;
  
  for(uint8_t index=0; index<nNodes; index++)
  {
    if(isNodeLinked(index))
    {
      nodes[linkedNodes] = index;
      linkedNodes++;
    }
  }

  return linkedNodes;
}

/**********************************************************************
 * @brief Return the linked state of a node
 * 
 * @param nodeAddress: address of the remote node. Range: [0..7]
 * @return: true if the node is linked; false if not
 */
bool isNodeLinked(uint8_t nodeAddress)
{
  return t2t_node[nodeAddress].linked;
}

/**********************************************************************
 * @brief Return the linked state of the main node
 * 
 * @return: true if the main node is linked; false if not
 */
bool isMainNodeLinked(void)
{
  return mainNode->linked;
}

/**********************************************************************
 * @brief Return the linked state of the working nodes. This function
 * is called when the node acts like the main one to check that the
 * comm with every working node is alive.
 * 
 * @return: true if all of the working nodes are linked; false if not
 */
bool isEveryWorkingNodeLinked(void)
{
  for(uint8_t index=0; index<nNodes; index++)
  {
    if(&t2t_node[index] != thisNode && t2t_node[index].working && !t2t_node[index].linked)
      return false;
  }
  
  return true;
}

/**********************************************************************
 * @brief Call the function to set the message to send with the time of
 * detection and set the options to try again some more time in case
 * that any answer isn't received.
 * 
 * @param sensor_detection_time: time of detection in milliseconds
 */
void sendDetectionMsg(uint32_t sensor_detection_time)
{
  sendESPNowDetectionMsg2MainNode(sensor_detection_time);

  detection_time = sensor_detection_time;
  detection_waiting4response = true;
  last_detectionMsg_Tx = get_currentTimeMs();
}

/**********************************************************************
 * @brief Return the time to show received from the main node and clear
 * the flag to avoid reading it again. This function is only called by
 * a secondary node.
 * 
 * @param: beep sound to make by the secondary node
 * @return: time to show if it has been received; -1 if no time
 *          storaged
 */
int32_t getTime2show(uint8_t *beep_sound)
{
  int32_t t = -1;
  
  if(flag_timeRx)
  {
    t = time2show;
    *beep_sound = beep;
  }

  flag_timeRx = false;
  return t;
}

/**********************************************************************
 * @brief Check if there are any detections received pending of being
 * processed. This function is only used by the main node.
 *
 * @return: true if there are detections pending; false if not
 */
bool isAnyDetectionRxPending(void)
{
  return (nextDetRx2write != nextDetRx2read);
}

/**********************************************************************
 * @brief Get time and address of the secondary node for the next
 * detection received to be processed. This function is only used by
 * the main node.
 *
 * @param secondaryNodeAddress: address of the secondary node that
 *                              sends the message
 * @return: 0 if no detections pending; a positive number if yes
 */
uint32_t getNextTimeDetectionRx(uint8_t *secondaryNodeAddress)
{
  uint32_t nextTimeDetection = 0;

  if(isAnyDetectionRxPending())
  {
    *secondaryNodeAddress = bufferDetectionMsgRx[nextDetRx2read].nodeAddr;
    nextTimeDetection = bufferDetectionMsgRx[nextDetRx2read].detectionTime;
    nextDetRx2read++;
    nextDetRx2read = nextDetRx2read % (sizeof(bufferDetectionMsgRx)/sizeof(bufferDetectionMsgRx[0]));
  }

  return nextTimeDetection;
}

/**********************************************************************
 * @brief Ignores any received detection pending of being processed
 */
void ignoreAnyDetectionRxPending(void)
{
  nextDetRx2read = nextDetRx2write;
}

/**********************************************************************
 * @brief Sends an ESPNow message to a secondary node with the time to
 * show on its display. Only called by a main node.
 * 
 * @param nodeAddress: address of the remote node. Range: [0..7]
 * @param beep: to order the secondary node make the beep sound.
 *              No beep = 0; simple beep = 1; double beep = 2
 * @param time2show: time to show on the secondary node's display, in
 *                   milliseconds
 */
void sendESPNowTimeMsg2MainNode(uint8_t nodeAddress, uint8_t beep, uint32_t time2show)
{
  uint8_t t_minutes = 0;
  uint16_t t_milliseconds = 0;

  t_milliseconds = (uint16_t)(time2show % 60000);
  t_minutes = (uint8_t)(time2show - t_milliseconds)/60000;
  
  s_espnow_time_msg msg;
  msg.type = (uint8_t)TIME_MSG;
  msg.beep = beep;
  msg.time2show_min = t_minutes;
  msg.time2show_msec = t_milliseconds;

  (void)esp_now_send(t2t_node[nodeAddress].MACAddr, (uint8_t *) &msg, sizeof(msg));
}

/**********************************************************************
 * @brief Sends an ESPNow message to the main node with a low battery
 * warning. The message includes the voltage of the battery.
 * 
 * @param battLow_flag: true if the battery is undervoltage; false if not
 * @param battVoltage: voltage of the battery (millivolts)
 */
void sendESPNowLowBattMsg2MainNode(bool battLow_flag, uint16_t battVoltage)
{
  s_espnow_lowBattery_msg msg;
  msg.type = (uint8_t)LOWBATTERY_MSG;
  msg.lowBatt = battLow_flag? 1 : 0;
  msg.battVoltage = (uint8_t)((battVoltage - 2700)/100);

  (void)esp_now_send(mainNode->MACAddr, (uint8_t *) &msg, sizeof(msg));
}

/**********************************************************************
 * @brief Check by seing the flag_modeReq matrix if all the nodes have
 * accepted the request sended previously
 * 
 * @return: 1 for acceptance completed; 0 for acceptance uncompleted;
 *          -1 for acceptance rejected
 */
int8_t isAcceptanceCompleted(void)
{
  if(modeRejected)
    return ACCEPTANCE_REJECTED;

  for(uint8_t index=0; index<nNodes; index++)
  {
    if(&t2t_node[index] != thisNode && flag_modeReq[index] != 0)
      return ACCEPTANCE_UNCOMPLETED;
  }

  return ACCEPTANCE_COMPLETED;
}

/**********************************************************************
 * @brief Returns the mode to join when this is the secondary node
 * 
 * @return: 0 or greater if this is a secondary node; -1 if not
 */
int8_t getMode2Join(void)
{
  if(thisNode == mainNode) // Error! This function must be called only by a secondary node
    return -1;

  return mode2join;
}

/**********************************************************************
 * @brief Configure this node (main) and the secondary nodes as working
 * in a mode
 * 
 * @param t2t_mode: mode requested
 * @param remoteNodeList: pointer to a list that includes the addresses 
 *                        of the remote nodes to join the mode
 * @param numRemoteNodes: number of remote nodes to join the mode
 */
void configNodes4WorkingMode(uint8_t t2t_mode, uint8_t *remoteNodeList, uint8_t numRemoteNodes)
{
  modeRejected = false;
  mode2join = t2t_mode;
  
  for(uint8_t index=0; index<numRemoteNodes; index++)
    flag_modeReq[remoteNodeList[index]] = 1;
}

/**********************************************************************
 * @brief Release the node while leaving a working mode. This allows
 * the node to control itself again. If this is the main node, send a
 * message to each node working with this one to release them.
 */
void releaseWorkingModeComm(void)
{
  if(thisNode == mainNode)
  {
    for(uint8_t index=0; index<nNodes; index++)
    {
      if(&t2t_node[index] != thisNode && t2t_node[index].working)
      {
        sendESPNowModeMsg(t2t_node[index].nodeAddress, 0, 0); // Send a message to release the remote node
        t2t_node[index].working = false;
      }
      flag_modeReq[index] = 0; // Clear a possible mode flag
    }
  }
  else
  {
    clear_led_time_offset();
    mainNode->working = false;
    mainNode = thisNode;
  }

  setThisNodeAsIdle();
  t_origen_ms = get_currentTimeMs(); // Allows link with other nodes after leaving a mode
}

/**********************************************************************
 * @brief Set this node as busy by setting the working flag
 */
void setThisNodeAsBusy(void)
{
  thisNode->working = true;
}

/**********************************************************************
 * @brief Controls the ESPnow periodical communication. This function
 * has to be called periodically through an scheduler.
 */
void espnow_task(void)
{
  // Check incoming messages
  if(nextMsgBuff2write != nextMsgBuff2read)
  {
    uint8_t nodeAddress = 0;
    uint8_t msgLength = 0;

    s_espnow_default_msg defaultMsg;

    nodeAddress = rxBuffer[nextMsgBuff2read].nodeAddr;
    msgLength = rxBuffer[nextMsgBuff2read].msgLength;
    memcpy(&defaultMsg, rxBuffer[nextMsgBuff2read].msg, 1);
    
    t2t_node[nodeAddress].linked = true;
    t2t_node[nodeAddress].lastRxTime_ms = rxBuffer[nextMsgBuff2read].rxTime;

    switch(defaultMsg.type)
    {
      case LINK_MSG:
        s_espnow_link_msg msg_link;
        memcpy(&msg_link, rxBuffer[nextMsgBuff2read].msg, msgLength);
        
        if(msg_link.ack && mainNode == &t2t_node[nodeAddress]) // If the remote node asks for an ACK, send a link msg with the ACK flag set
          sendESPNowLinkMsg(nodeAddress, true);
        else if(!msg_link.ack && t2t_node[nodeAddress].working && mainNode == thisNode) // The secondary node has been reseted and it is out of the mode
          t2t_node[nodeAddress].linked = false;
        break;

      case MODE_MSG:
        s_espnow_mode_msg msg_mode;
        memcpy(&msg_mode, rxBuffer[nextMsgBuff2read].msg, msgLength);

        if(msg_mode.request) // Request to join
        {
          if(thisNode == mainNode && !thisNode->working)
          {
            sendESPNowModeMsg(nodeAddress, msg_mode.request, 0); // Send ACK accepting the request
            set_led_time_offset(t2t_node[nodeAddress].lastRxTime_ms, (uint16_t)msg_mode.ref_time);
            setThisNodeAsBusy();
            mainNode = &t2t_node[nodeAddress];
            mainNode->working = true;
            mode2join = msg_mode.work_mode;
          }
        }
        else // Request accepted or release node
        {
          if(thisNode == mainNode && flag_modeReq[nodeAddress])
          {
            flag_modeReq[nodeAddress] = 0; // ACK received from the secondary node to accept the request
            t2t_node[nodeAddress].working = true;
          }
          else if(mainNode == &t2t_node[nodeAddress]) // This is a secondary node
          {
            releaseWorkingModeComm();
          }
        }
        break;
        
      case DETECTION_MSG:
        s_espnow_detection_msg msg_detection;
        memcpy(&msg_detection, rxBuffer[nextMsgBuff2read].msg, msgLength);

        bufferDetectionMsgRx[nextDetRx2write].nodeAddr = nodeAddress;
        bufferDetectionMsgRx[nextDetRx2write].detectionTime = t2t_node[nodeAddress].lastRxTime_ms - msg_detection.elapsed_time;
        nextDetRx2write++;
        nextDetRx2write = nextDetRx2write % (sizeof(bufferDetectionMsgRx)/sizeof(bufferDetectionMsgRx[0]));

        break;
        
      case TIME_MSG:
        s_espnow_time_msg msg_time;
        memcpy(&msg_time, rxBuffer[nextMsgBuff2read].msg, msgLength);

        if(mainNode == &t2t_node[nodeAddress])
        {
          beep = msg_time.beep;
          time2show = msg_time.time2show_min * 60000 + msg_time.time2show_msec;
          flag_timeRx = true;
          detection_waiting4response = false;
        }
      
        break;
        
      case LOWBATTERY_MSG:
        s_espnow_lowBattery_msg msg_lowBattery;
        memcpy(&msg_lowBattery, rxBuffer[nextMsgBuff2read].msg, msgLength);

        //todo: if this node is controlling the node that sends the battery msg, redirect it to the remote device (PC or mobile App)

        break;

      default:
        break;
    }

    nextMsgBuff2read += 1;
    nextMsgBuff2read = nextMsgBuff2read % (sizeof(rxBuffer)/sizeof(s_rxBuffer));
  }

  // Check periodical communication and ACK messages
  linking_management();

  if(thisNode == mainNode) // If this is the main node, manage mode messages
    mode_request_management(); // Send mode requests and check acceptances
  else // thisNode != mainNode
    detection_time_management(); // Check the required retransmissions of the detection messages
}
