Resaj/time2time/fw/FW_basic/Crushed_Regular_65.h

// Created by http://oleddisplay.squix.ch/ Consider a donation
// In case of problems make sure that you are using the font file with the correct version!
const unsigned char Crushed_Regular_65[] PROGMEM = {
  0x31, // Width: 49
  0x4B, // Height: 75
  0x20, // First Char: 32
  0xE0, // Numbers of Chars: 224

  // Jump Table:
  0xFF, 0xFF, 0x00, 0x0D,  // 32:65535
  0x00, 0x00, 0x62, 0x0D,  // 33:0
  0x00, 0x62, 0x86, 0x10,  // 34:98
  0x00, 0xE8, 0x112, 0x1E,  // 35:232
  0x01, 0xFA, 0xD9, 0x18,  // 36:506
  0x02, 0xD3, 0x147, 0x22,  // 37:723
  0x04, 0x1A, 0x12A, 0x1F,  // 38:1050
  0x05, 0x44, 0x36, 0x08,  // 39:1348
  0x05, 0x7A, 0x9E, 0x12,  // 40:1402
  0x06, 0x18, 0x92, 0x12,  // 41:1560
  0x06, 0xAA, 0xAE, 0x14,  // 42:1706
  0x07, 0x58, 0x131, 0x24,  // 43:1880
  0x08, 0x89, 0x4E, 0x0A,  // 44:2185
  0x08, 0xD7, 0x9B, 0x13,  // 45:2263
  0x09, 0x72, 0x4E, 0x0A,  // 46:2418
  0x09, 0xC0, 0x8E, 0x10,  // 47:2496
  0x0A, 0x4E, 0x100, 0x1C,  // 48:2638
  0x0B, 0x4E, 0x6C, 0x10,  // 49:2894
  0x0B, 0xBA, 0xD0, 0x17,  // 50:3002
  0x0C, 0x8A, 0xD9, 0x18,  // 51:3210
  0x0D, 0x63, 0x100, 0x1B,  // 52:3427
  0x0E, 0x63, 0xE3, 0x18,  // 53:3683
  0x0F, 0x46, 0xF7, 0x1B,  // 54:3910
  0x10, 0x3D, 0xCB, 0x16,  // 55:4157
  0x11, 0x08, 0xF7, 0x1B,  // 56:4360
  0x11, 0xFF, 0xF5, 0x1B,  // 57:4607
  0x12, 0xF4, 0x58, 0x0C,  // 58:4852
  0x13, 0x4C, 0x58, 0x0C,  // 59:4940
  0x13, 0xA4, 0x133, 0x24,  // 60:5028
  0x14, 0xD7, 0x128, 0x24,  // 61:5335
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
};
