Resaj/time2time/fw/t2t_fw/buttons.cpp

/**********************************************************************
 * Project: Time2time
 * 
 * File description: This code file contains the parameters and 
 * functions for reading the state of the buttons
 * 
 * Author: Rubén Espino San José
 * Puma Pride Robotics Team
 * 
 * License: Attribution-NonCommercial-ShareAlike 4.0
 * International (CC BY-NC-SA 4.0) 
 *********************************************************************/

/**********************************************************************
 * Includes
 *********************************************************************/

#include "Arduino.h"
#include "config/PINSEL.h"
#include "buttons.h"
#include "scheduler.h"

/**********************************************************************
 * Configuration parameters
 *********************************************************************/

#define INVERTED        0   // Button logic: actived when output is 0
#define NON_INVERTED    1   // Button logic: actived when output is 1

#define FILTERING_TIME  50u  // Minimum time in ms with button actived to filter voltage noise

/**********************************************************************
 * Structs
 *********************************************************************/

typedef struct {
  uint8_t pin;          // uC pin connected to the button
  uint8_t raw_state;    // Button state (read directly from the pin)
  uint8_t level_state;  // Button level signal state filtered: 1 = HIGH; 0 = LOW
  uint8_t edge_state;   // Button edge signal state filtered: 1 = rising edge; 0 = rest of cases
  uint8_t logic;        // Button logic
  uint32_t time_flag;   // Filtering time flag
  bool detection_flag;  // Continuous detection avoidance flag
} s_button;

/**********************************************************************
 * Local variables
 *********************************************************************/

s_button button_A = {PIN_BUTTON_A, 0, 0, 0, INVERTED, 0, 0};
s_button button_B = {PIN_BUTTON_B, 0, 0, 0, INVERTED, 0, 0};
s_button button_C = {PIN_BUTTON_C, 0, 0, 0, INVERTED, 0, 0};

s_button *buttons[3];

/**********************************************************************
 * Local function declarations
 *********************************************************************/

void read_button(s_button *button);

/**********************************************************************
 * Local functions
 *********************************************************************/

/**********************************************************************
 * @brief Reads the status of the buttons
 * 
 * @param button: struct data of button which is going to be read
 */
void read_button(s_button *button)
{
  button->raw_state = (button->logic == INVERTED)? !digitalRead(button->pin) : digitalRead(button->pin);

  /* Filter voltage noise */
  if(button->raw_state)
  {
    if(get_currentTimeMs() - button->time_flag >= FILTERING_TIME)
      button->level_state = button->raw_state;
  }
  else
  {
    button->level_state = button->raw_state;
    button->time_flag = get_currentTimeMs();
  }

  /* Avoid continuos detection */
  button->edge_state = (button->level_state && button->detection_flag) ? 1 : 0;
  button->detection_flag = button->level_state ? false : true;
}

/**********************************************************************
 * Global functions
 *********************************************************************/

/**********************************************************************
 * @brief Configures the pins of buttons as inputs
 */
void buttons_init(void)
{
  pinMode(button_A.pin, INPUT);
  pinMode(button_B.pin, INPUT);
  pinMode(button_C.pin, INPUT);

  buttons[0] = &button_A;
  buttons[1] = &button_B;
  buttons[2] = &button_C;
}

/**********************************************************************
 * @brief Reads all the button status and storages them locally. This 
 * function has to be called periodically through an scheduler
 */
void buttons_task(void)
{
  for(uint8_t i=0; i<sizeof(buttons)/sizeof(s_button*); i++)
    read_button(buttons[i]);
}

/**********************************************************************
 * @brief returns the button state. 1 = actived; 0 = unactived
 * 
 * @param button_number: the number of the button to be read
 * @returns battery voltage (volts * 1000)
 */
uint8_t get_button_state(button_list button_number)
{
  return buttons[button_number]->edge_state;
}
