Resaj/time2time/fw/t2t_fw/t2t_data.h

/**********************************************************************
 * Project: Time2time
 * 
 * File description: This header file contains general information
 * related to the t2t firmware
 * 
 * Author: Rubén Espino San José
 * Puma Pride Robotics Team
 * 
 * License: Attribution-NonCommercial-ShareAlike 4.0
 * International (CC BY-NC-SA 4.0) 
 *********************************************************************/

#ifndef T2T_DATA_H
#define T2T_DATA_H

/**********************************************************************
 * Defines
 *********************************************************************/

#define FW_VERSION "V1.1.1"

#endif /* T2T_DATA_H */
