Resaj/time2time/fw/t2t_test/config/PINSEL.h

/*****************************************************
 * Project: Time2time
 * 
 * File description: This file contains the pins
 * configurations for the peripherals connected to the
 * microcontroller.
 * 
 * Author: Rubén Espino San José
 * Puma Pride Robotics Team
 * 
 * License: Attribution-NonCommercial-ShareAlike 4.0
 * International (CC BY-NC-SA 4.0) 
 ****************************************************/

#ifndef PINSEL_H
#define PINSEL_H


#define PIN_UART_TX        1
#define PIN_UART_RX        3
#define PIN_BUZZER_PWM     4
#define PIN_LED_R          5
#define PIN_LED_G         14
#define PIN_LED_B         15
#define PIN_SLEEP_12V     12
#define PIN_EXP1          13
#define PIN_EXP2          16
#define PIN_EXP3          23
#define PIN_EXP4          25
#define PIN_EXP5          26
#define PIN_POWER_GOOD    17
#define PIN_STAT1         18
#define PIN_STAT2         19
#define PIN_I2C_SDA_DISP  21
#define PIN_I2C_SCL_DISP  22
#define PIN_SENSOR        27
#define PIN_BATT_MONITOR  32
#define PIN_JP_ADD1       33
#define PIN_JP_ADD2       34
#define PIN_JP_ADD3       35
#define PIN_BUTTON_A      36 // BUTTON_1
#define PIN_BUTTON_B      39 // BUTTON_2
#define PIN_BUTTON_C       0 // LOAD/BUTTON_3


#endif /* PINSEL_H */
